xbx1g/Robot/3D_Modeli/Robotska_roka/41002457.jpg

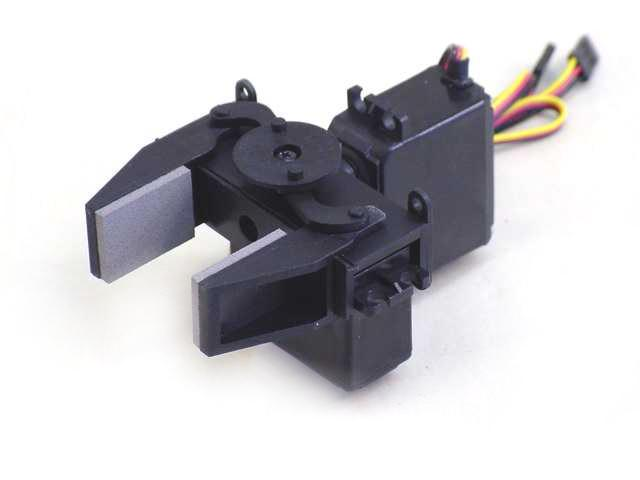
3D_Modeli/Robotska_roka/41002457.jpg
