xbx1g/Robot/3D_Modeli/Robotska_roka/lemotech-ip67-junction-box-250-mm-x-150-mm-x-100-mm-1.snapshot.2/LeMotech IP67 Junction Box, 250 mm x 150 mm x 100 mm D.JPG

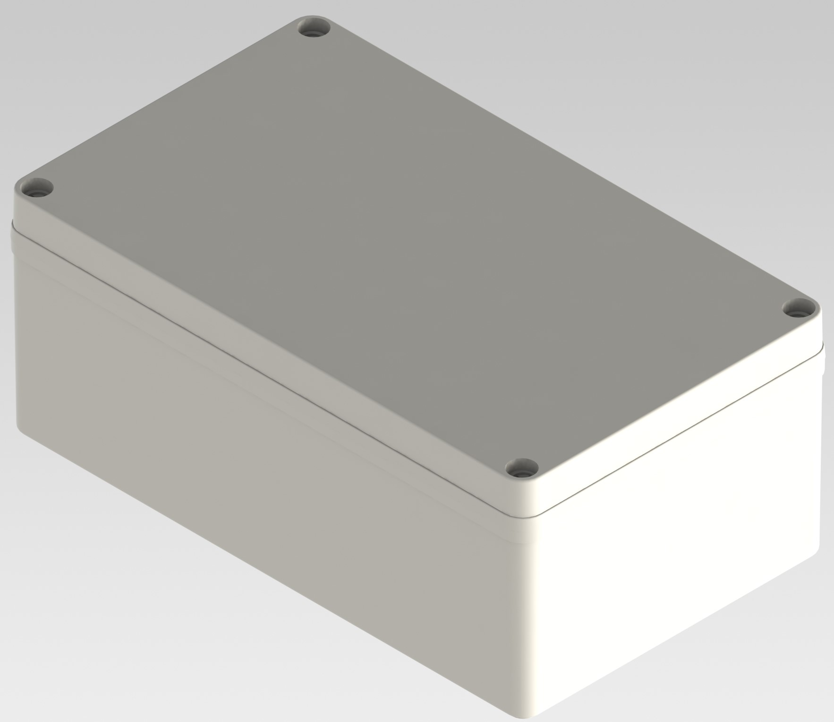
3D_Modeli/Robotska_roka/lemotech-ip67-junction-box-250-mm-x-150-mm-x-100-mm-1.snapshot.2/LeMotech IP67 Junction Box, 250 mm x 150 mm x 100 mm D.JPG
