xbx1g/Robot/3D_Modeli/Robotska_roka/linear-gripper-1.snapshot.4/CAD Model.png

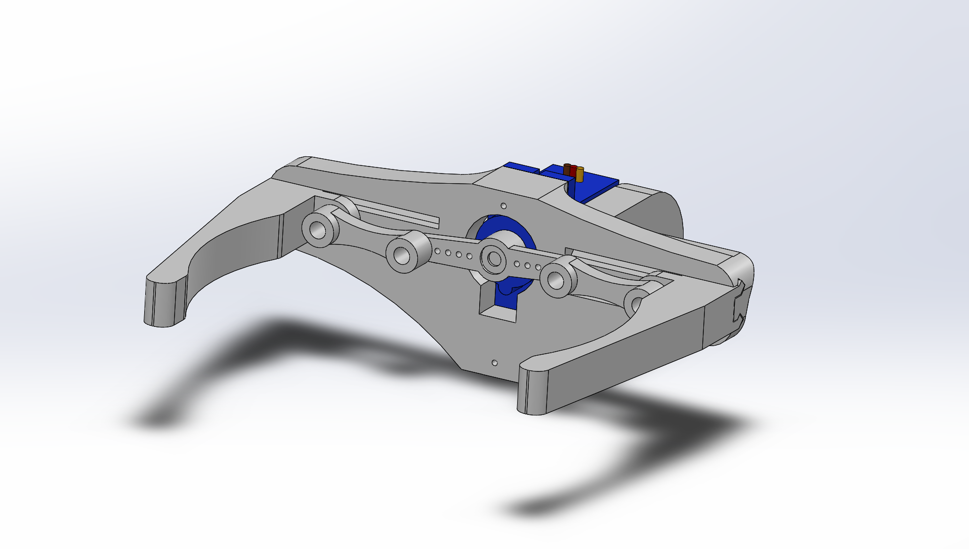
3D_Modeli/Robotska_roka/linear-gripper-1.snapshot.4/CAD Model.png
