xbx1g/Robot/3D_Modeli/Robotska_roka/mecanum-wheel-diameter-100mm-right-1.snapshot.1/Mecanum Wheel (dia 100) Right/Mecanum Wheel (dia 100).jpg

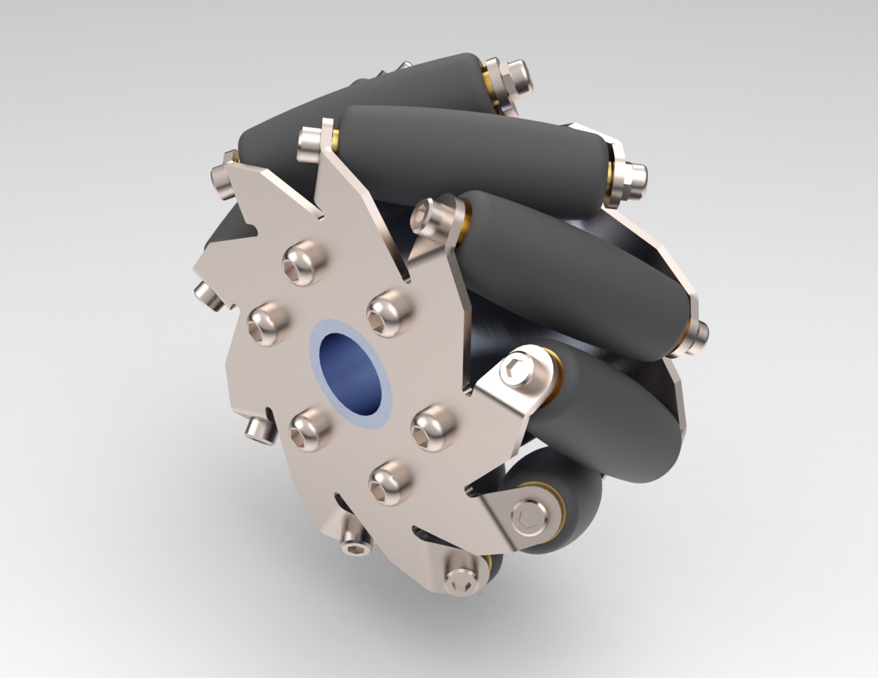
3D_Modeli/Robotska_roka/mecanum-wheel-diameter-100mm-right-1.snapshot.1/Mecanum Wheel (dia 100) Right/Mecanum Wheel (dia 100).jpg
