xbx1g/Robot/Aplikacija/APP INVENTRO/desnogor.png

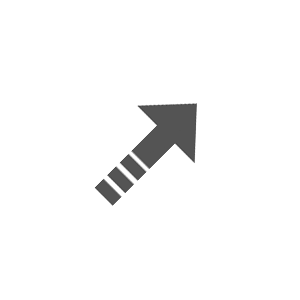
Aplikacija/APP INVENTRO/desnogor.png
