xbx1g/Robot/Aplikacija/APP INVENTRO/levodol.png

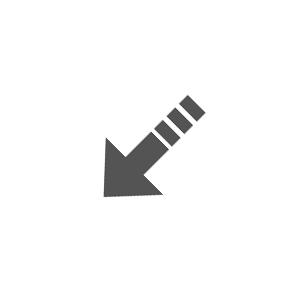
Aplikacija/APP INVENTRO/levodol.png
