xbx1g/Robot/Aplikacija/APP INVENTRO/levogor.png

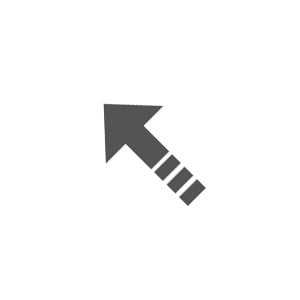
Aplikacija/APP INVENTRO/levogor.png
