xbx1g/Robot/Aplikacija/APP INVENTRO/ozadje.jpg

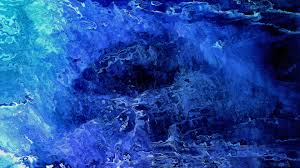
Aplikacija/APP INVENTRO/ozadje.jpg
