xbx1g/Robot/Aplikacija/APP INVENTRO/puscica desno.png

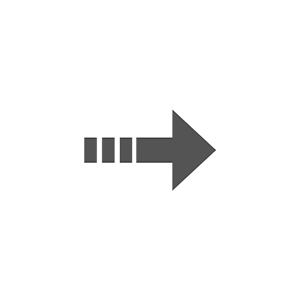
Aplikacija/APP INVENTRO/puscica desno.png
