xbx1g/Robot/Aplikacija/APP INVENTRO/puscica dol.png

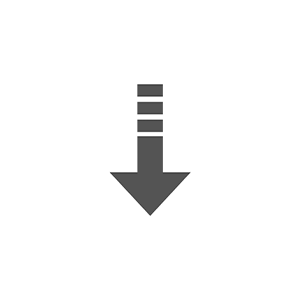
Aplikacija/APP INVENTRO/puscica dol.png
