xbx1g/Robot/Aplikacija/APP INVENTRO/puscica levo.png

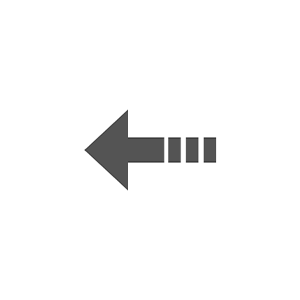
Aplikacija/APP INVENTRO/puscica levo.png
