xbx1g/Robot/Aplikacija/APP INVENTRO/roka.png

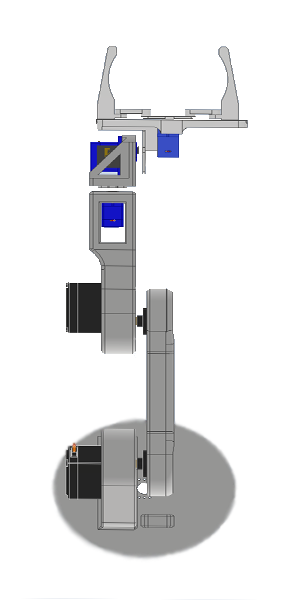
Aplikacija/APP INVENTRO/roka.png
