xbx1g/Robot/Aplikacija/APP INVENTRO/ROTACIJA DESNO.png

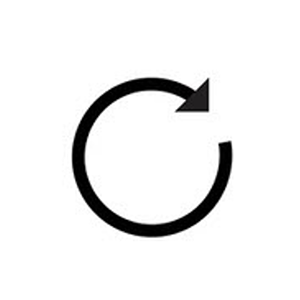
Aplikacija/APP INVENTRO/ROTACIJA DESNO.png
