xbx1g/Robot/Slike/IMG_20231021_095145.jpg

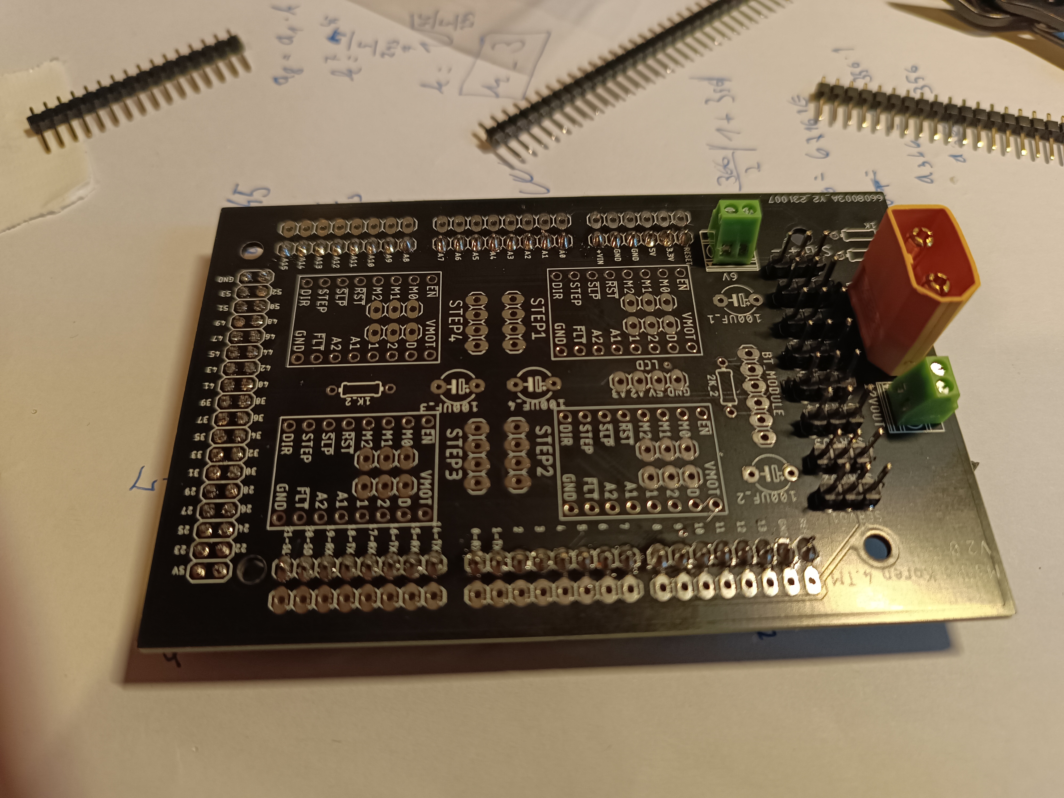
Slike/IMG_20231021_095145.jpg
