xbx1g/Robot/Slike/IMG_20231021_095151.jpg

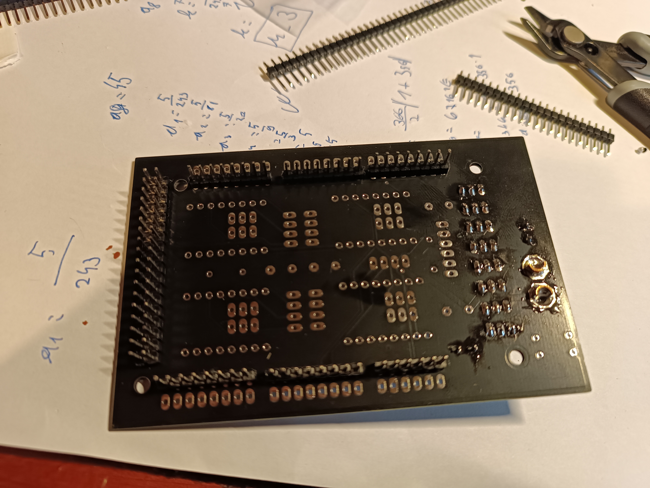
Slike/IMG_20231021_095151.jpg
