xbx1g/Robot/Slike/IMG_20231021_102045.jpg

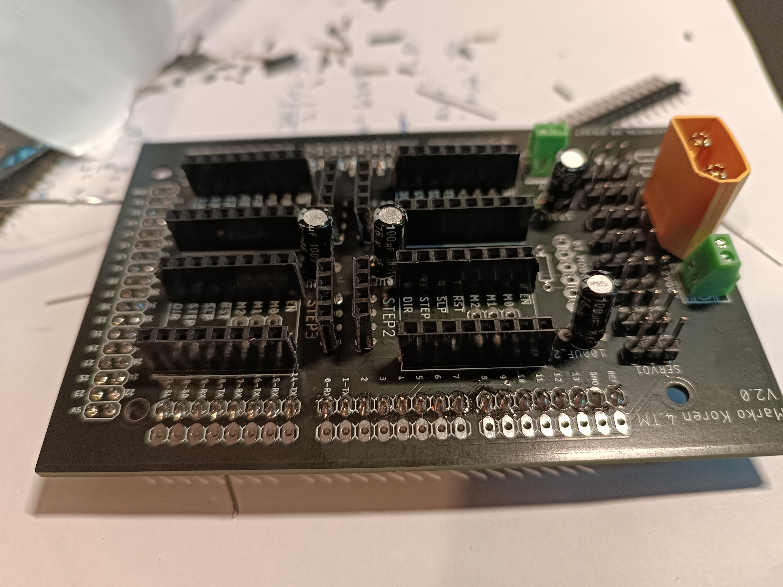
Slike/IMG_20231021_102045.jpg
