xbx1g/Robot/Slike/IMG_20231021_102051.jpg

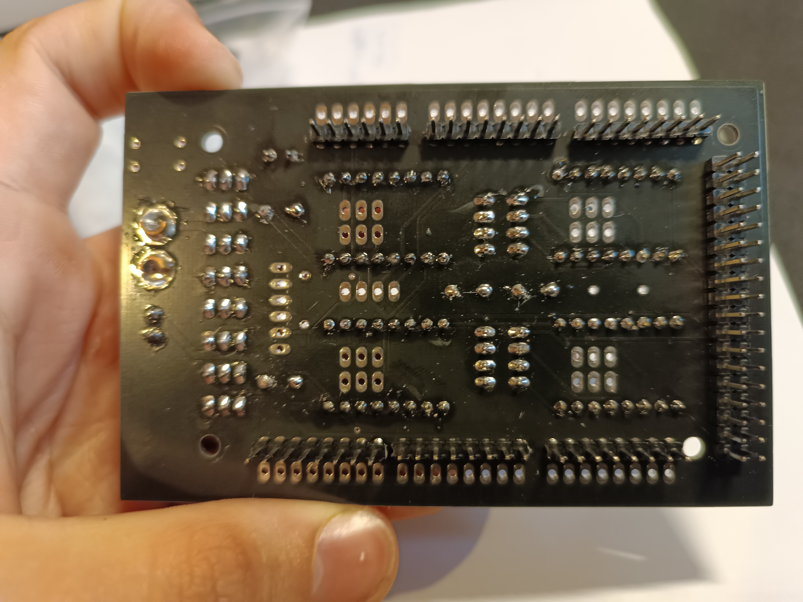
Slike/IMG_20231021_102051.jpg
