xbx1g/Robot/Slike/IMG_20231021_115019.jpg

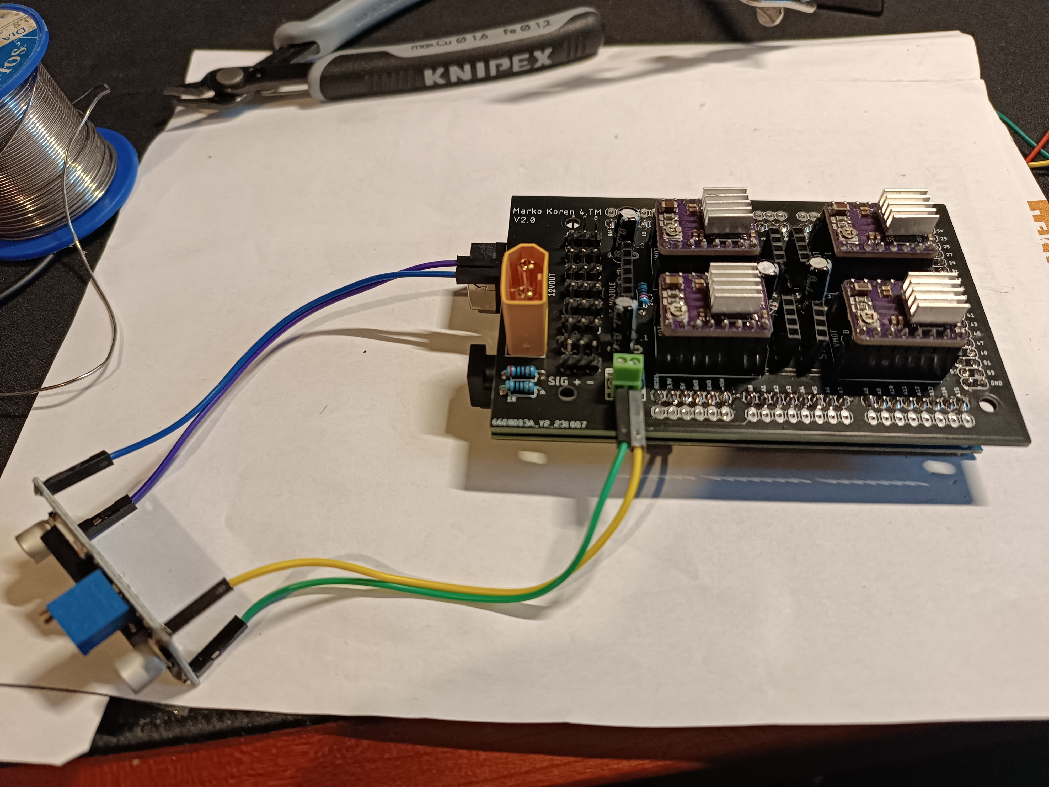
Slike/IMG_20231021_115019.jpg
