xbx1g/Robot/Slike/IMG_20231021_115023.jpg

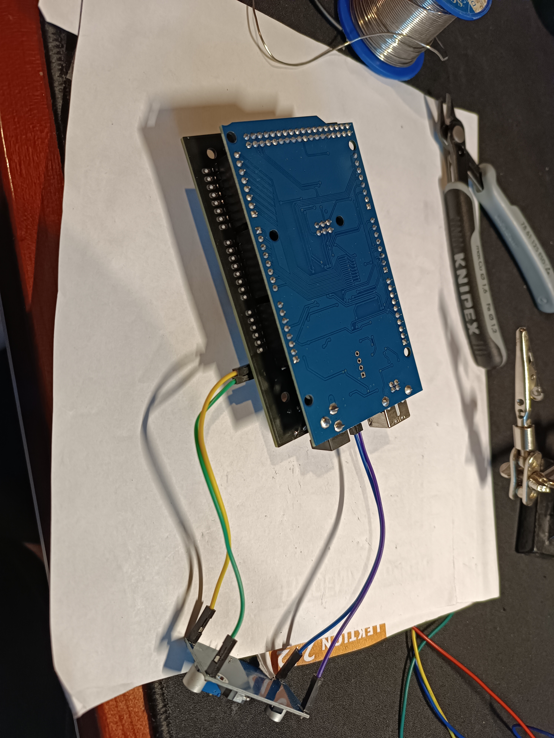
Slike/IMG_20231021_115023.jpg
