xbx1g/Robot/Slike/luknje_1.jpg

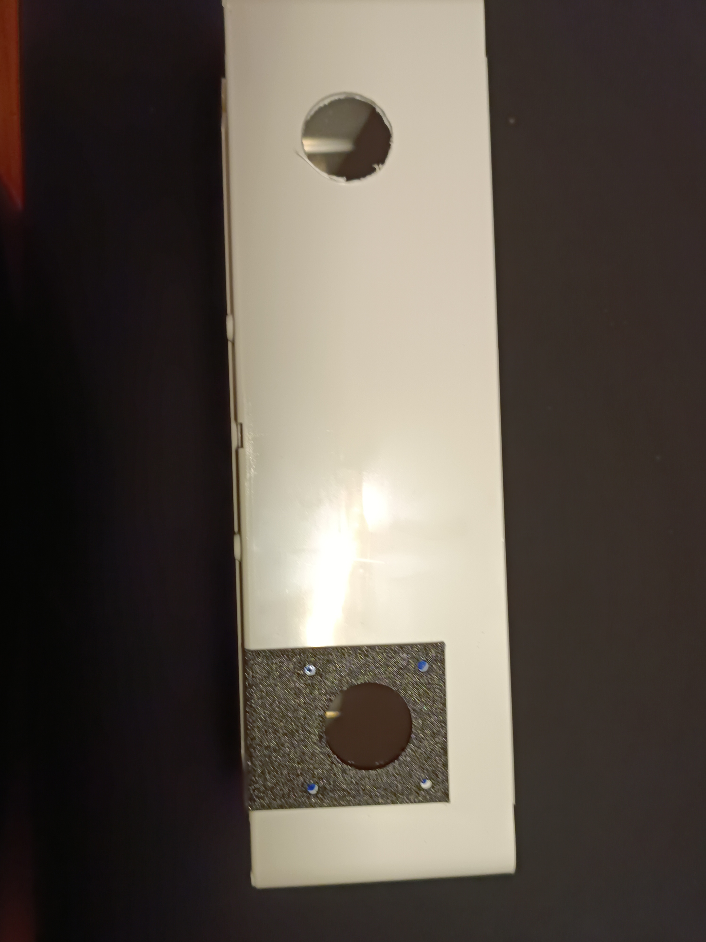
Slike/luknje_1.jpg
