xbx1g/Robot/Slike/luknje_2.jpg

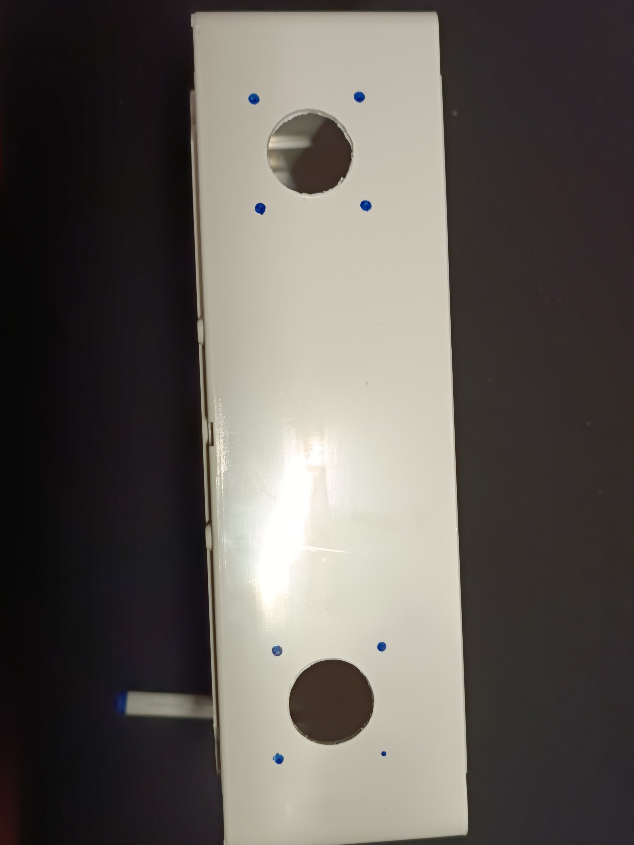
Slike/luknje_2.jpg
