xbx1g/Robot/Slike/luknje_3.jpg

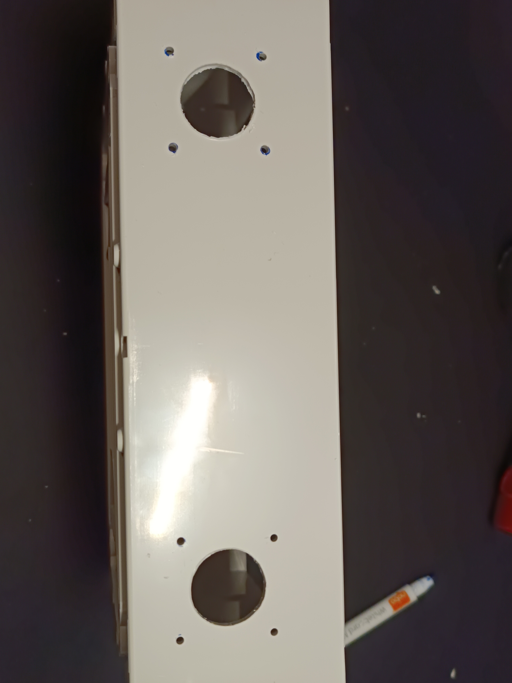
Slike/luknje_3.jpg
