xbx1g/Robot/Slike/pcb_cena.png

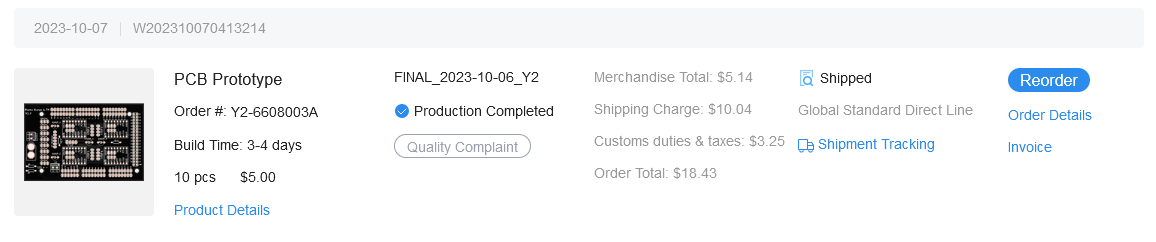
Slike/pcb_cena.png
