xbx1g/Robot/Slike/postavitev_podvozja.jpg

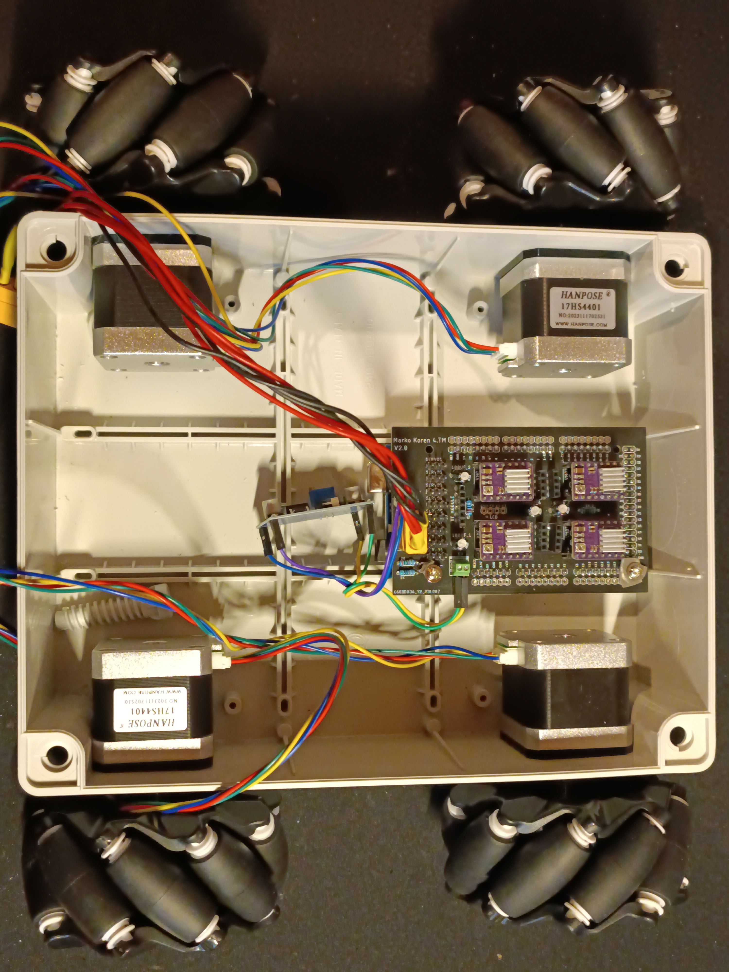
Slike/postavitev_podvozja.jpg
