xbx1g/Robot/Slike/Povezava_z_mecanum_kolesi.jpg

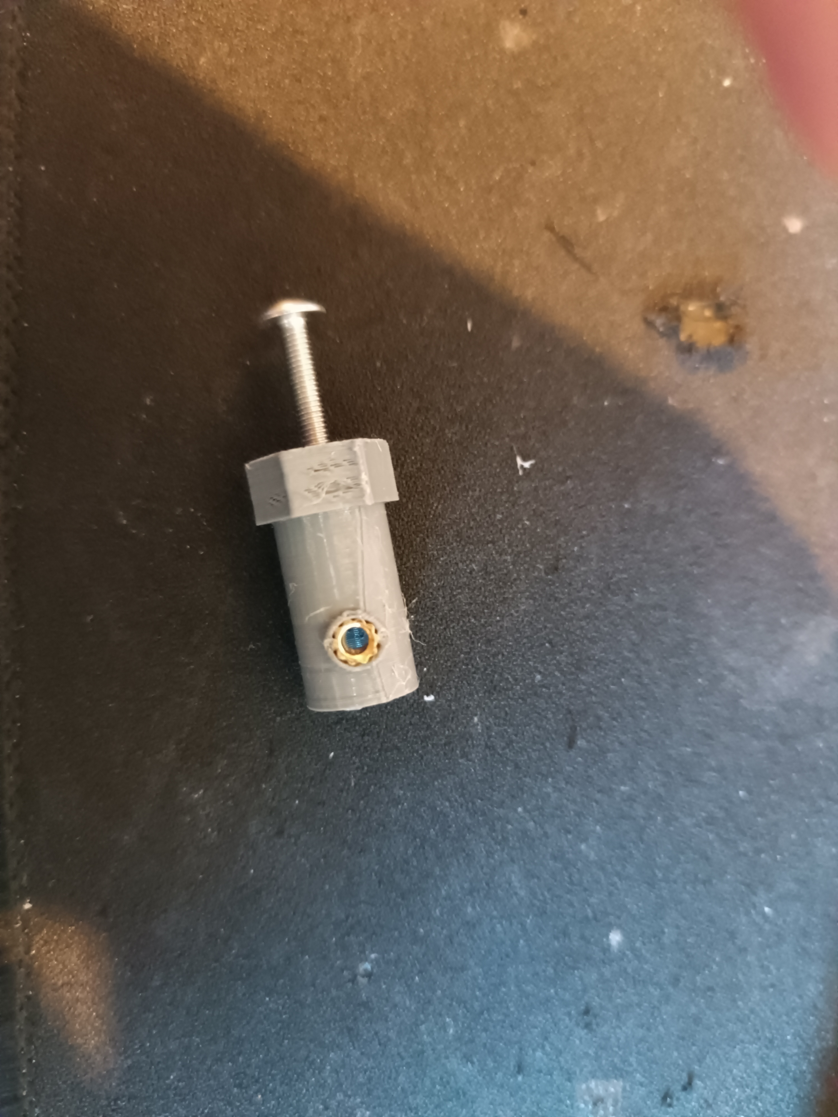
Slike/Povezava_z_mecanum_kolesi.jpg
