xbx1g/Robot/Slike/Robotska_roka_sestavljena (1).jpg

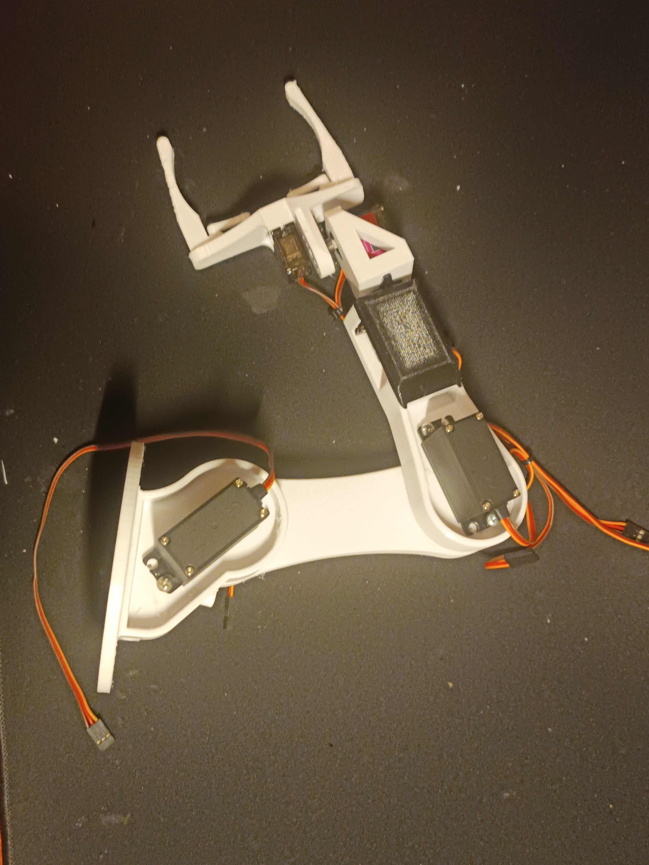
Slike/Robotska_roka_sestavljena (1).jpg
