xbx1g/Robot/Slike/Robotska_roka_sestavljena (2).jpg

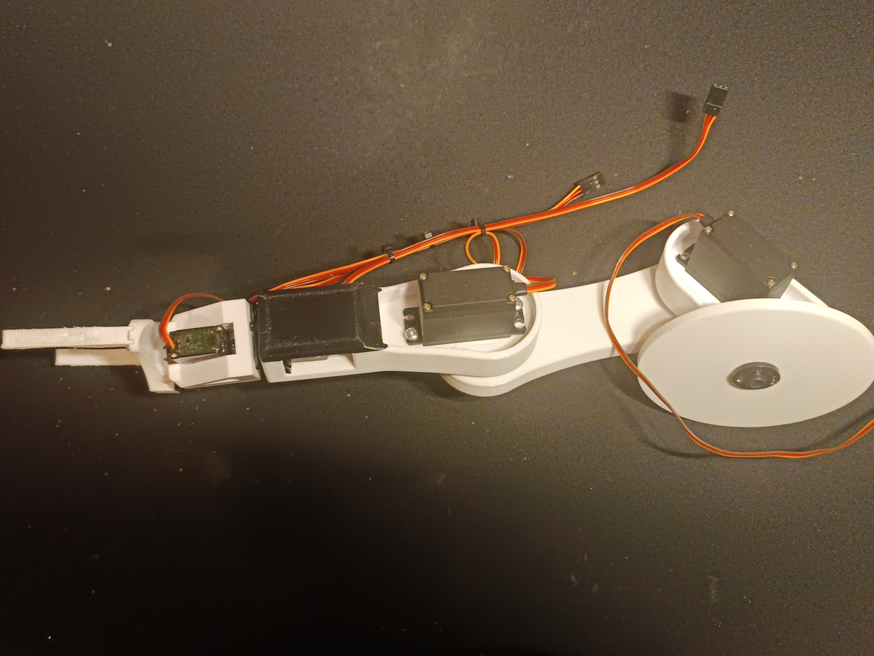
Slike/Robotska_roka_sestavljena (2).jpg
