xbx1g/Robot/Slike/Robotska_roka_sestavljena (3).jpg

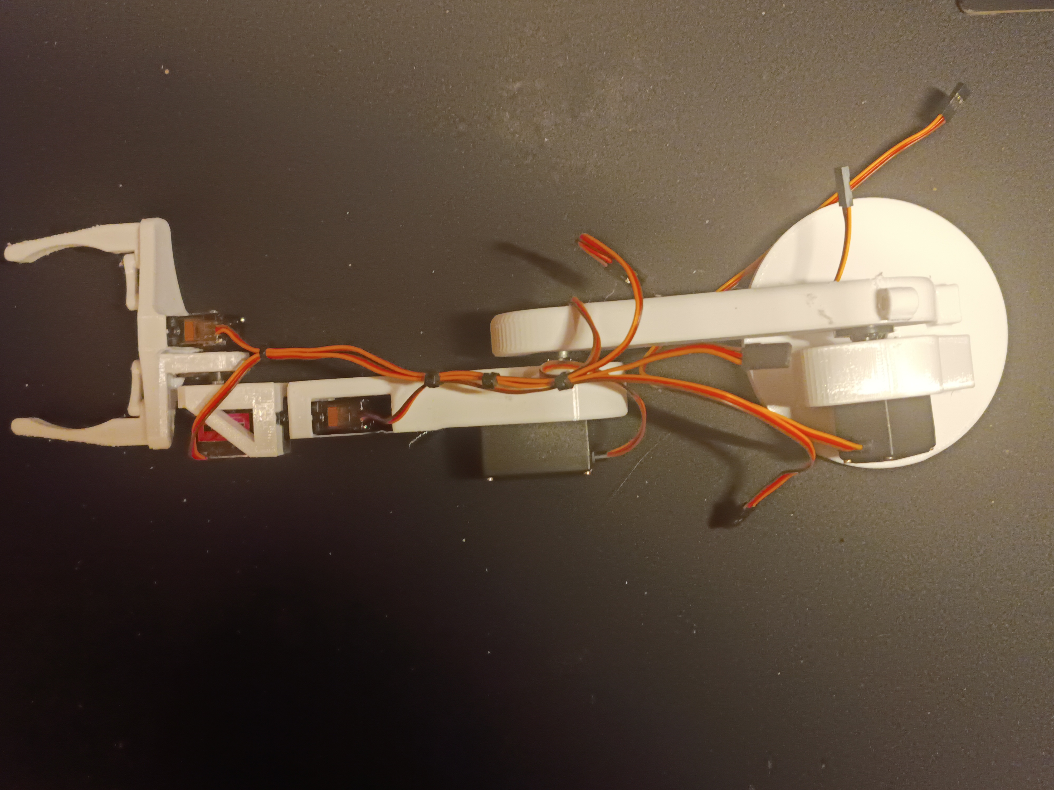
Slike/Robotska_roka_sestavljena (3).jpg
