xbx1g/Robot/Slike/spajanje_steper_motor.jpg

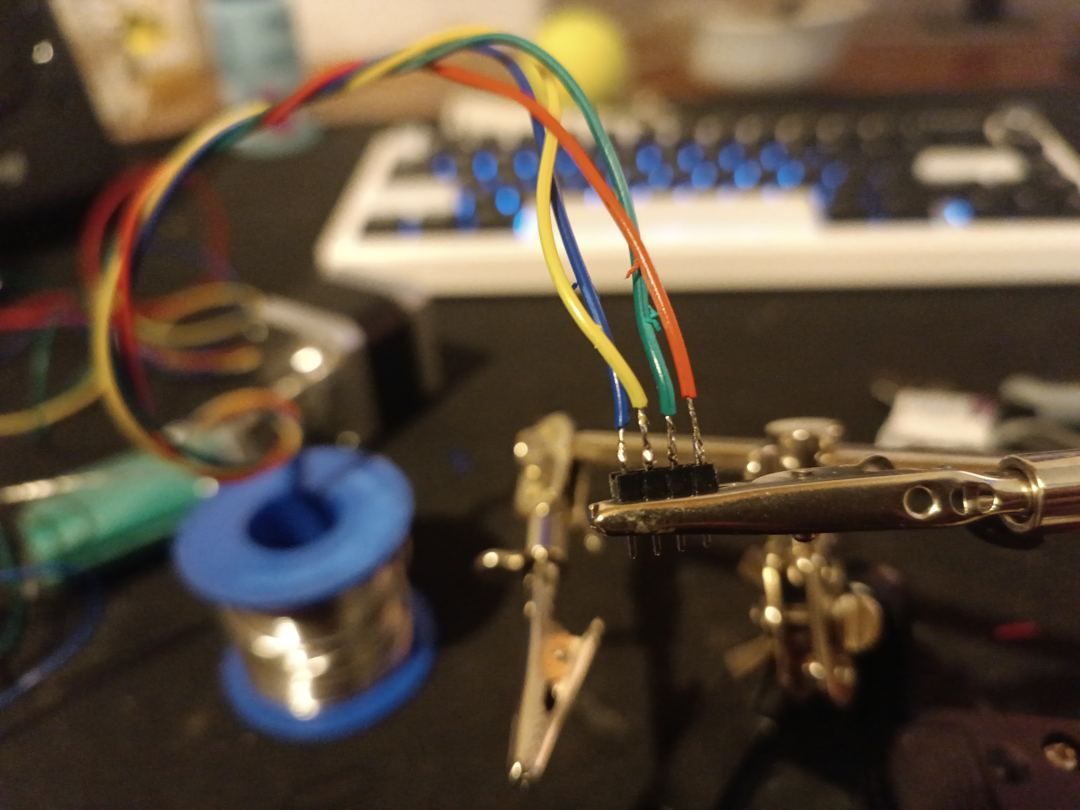
Slike/spajanje_steper_motor.jpg
