xbx1g/Robot/Slike/temperatura_30min.jpg

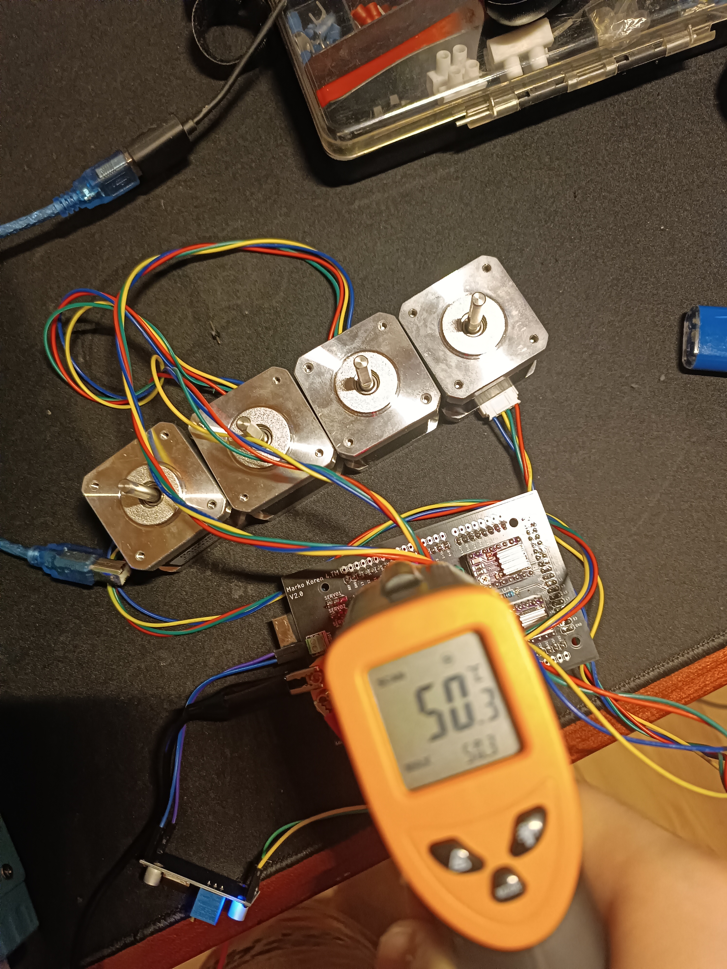
Slike/temperatura_30min.jpg
