xbx1g/Robot/3D_Modeli/VER2/roka2.stl

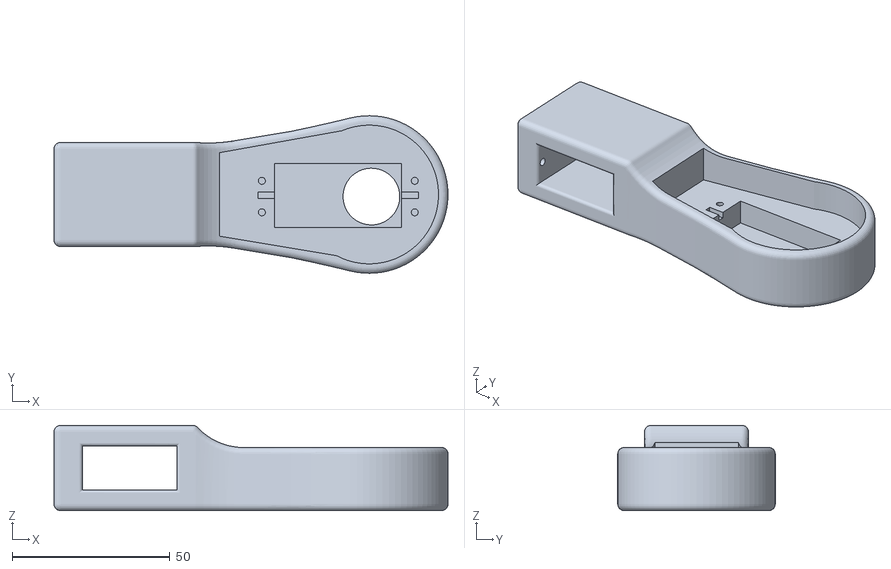
[picture p57: CAD file, 2025-09-28]
3D_Modeli/VER2/roka2.stl
125.0 x 50.0 x 27.0
