xbx1g/Robot/3D_Modeli/VER2/sg90-micro-servo-9g-tower-pro-1.snapshot.3/SG90 - Micro Servo 9g - Tower Pro.5.SLDPRT

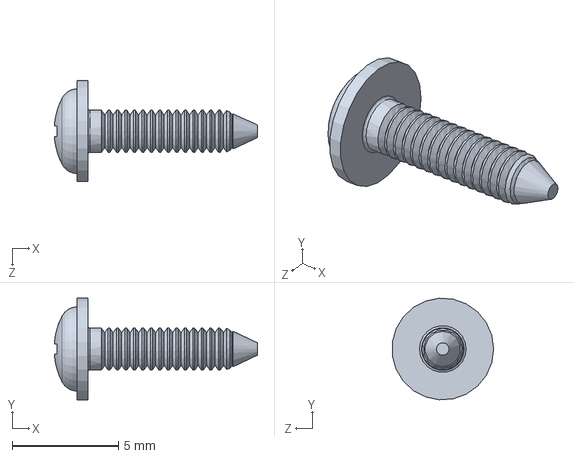
[picture p58: CAD file, 2025-09-28]
3D_Modeli/VER2/sg90-micro-servo-9g-tower-pro-1.snapshot.3/SG90 - Micro Servo 9g - Tower Pro.5.SLDPRT
9.57 x 4.79 x 4.78 mm
