xbx1g/Robot/3D_Modeli/Robotska_roka/123.stl

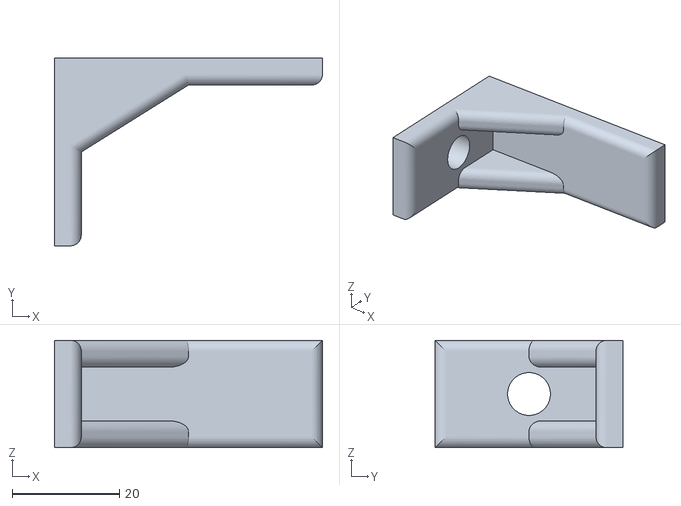
[picture p59: CAD file, 2025-09-28]
3D_Modeli/Robotska_roka/123.stl
50.0 x 35.0 x 20.0
