xbx1g/Robot/3D_Modeli/Robotska_roka/lemotech-ip67-junction-box-250-mm-x-150-mm-x-100-mm-1.snapshot.2/Cover, LeMotech IP67 Junction Box, 250 mm x 150 mm x 100 mm.SLDPRT

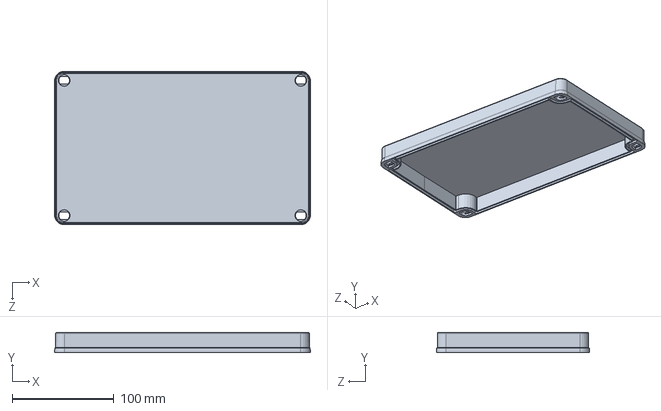
[picture p60: CAD file, 2025-09-28]
3D_Modeli/Robotska_roka/lemotech-ip67-junction-box-250-mm-x-150-mm-x-100-mm-1.snapshot.2/Cover, LeMotech IP67 Junction Box, 250 mm x 150 mm x 100 mm.SLDPRT
252.0 x 20.0 x 151.0 mm
