xbx1g/Robot/3D_Modeli/Robotska_roka/mecanum-wheel-diameter-100mm-right-1.snapshot.1/Mecanum Wheel (dia 100) Right/Components/Roller Bracket.SLDPRT

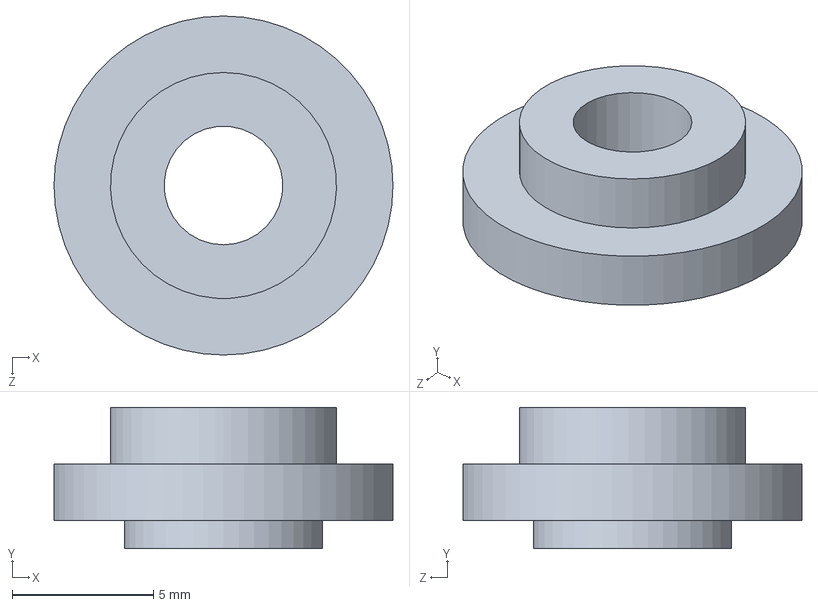
[picture p61: CAD file, 2025-09-28]
3D_Modeli/Robotska_roka/mecanum-wheel-diameter-100mm-right-1.snapshot.1/Mecanum Wheel (dia 100) Right/Components/Roller Bracket.SLDPRT
12.0 x 5.00 x 12.0 mm
