xbx1g/Robot/3D_Modeli/VER2/buh.stl

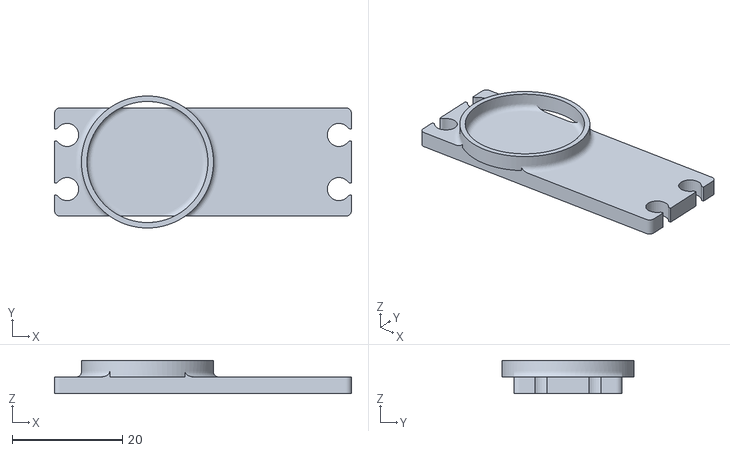
[picture p63: CAD file, 2025-09-28]
3D_Modeli/VER2/buh.stl
54.0 x 24.0 x 6.00
