xbx1g/Robot/3D_Modeli/VER2/linear-gripper-1.snapshot.4/Linear Gripper/Part1.stl

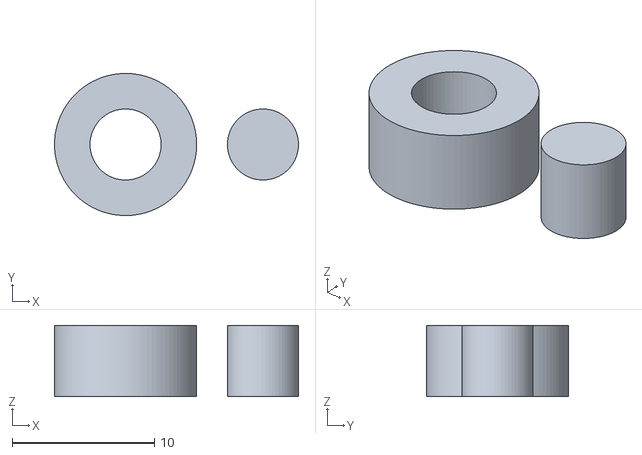
[picture p64: CAD file, 2025-09-28]
3D_Modeli/VER2/linear-gripper-1.snapshot.4/Linear Gripper/Part1.stl
17.2 x 10.00 x 5.00
