xbx1g/Robot/3D_Modeli/VER2/mecanum-wheel-diameter-100mm-right-1.snapshot.1/Mecanum Wheel (dia 100) Right/Components/Shaft.SLDPRT

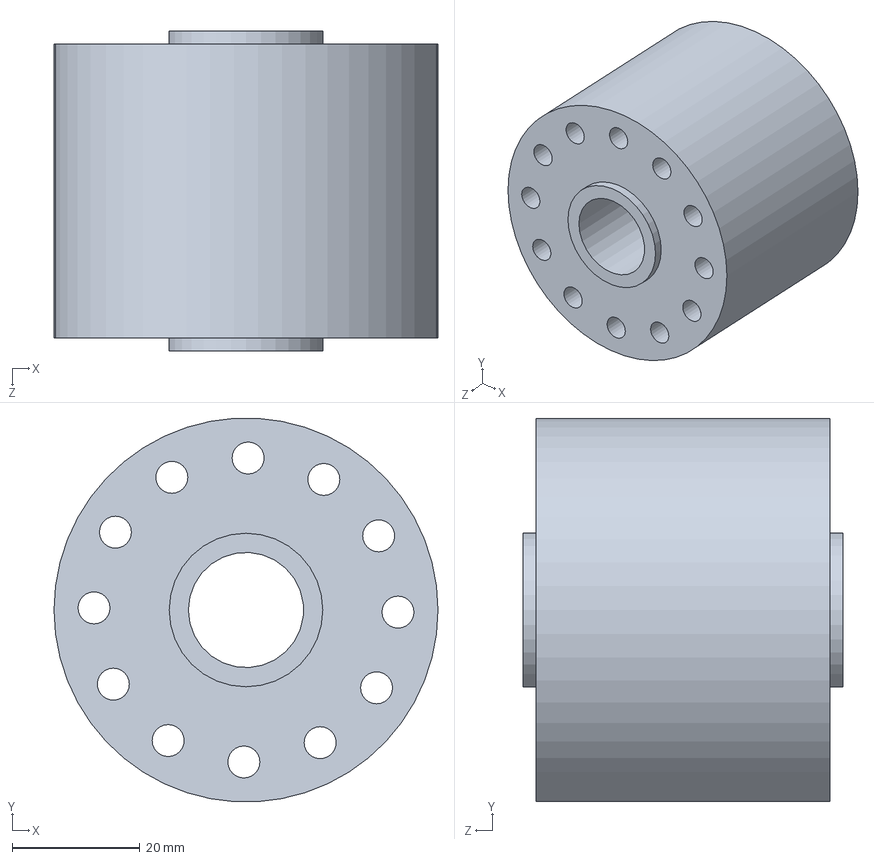
[picture p65: CAD file, 2025-09-28]
3D_Modeli/VER2/mecanum-wheel-diameter-100mm-right-1.snapshot.1/Mecanum Wheel (dia 100) Right/Components/Shaft.SLDPRT
60.0 x 59.9 x 50.0 mm
