xbx1g/Robot/3D_Modeli/Robotska_roka/linear-gripper-1.snapshot.4/Linear Gripper/Linear Base.stl

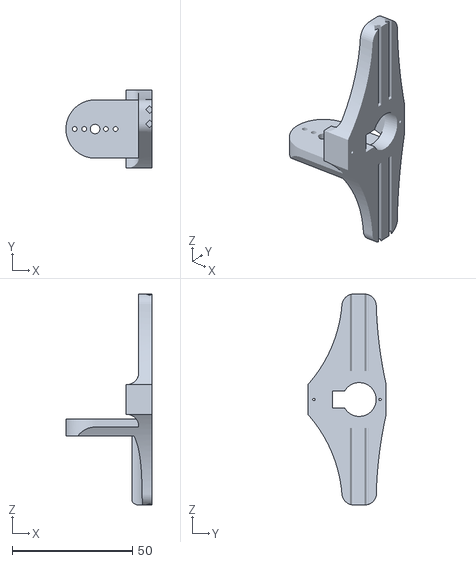
[picture p66: CAD file, 2025-09-28]
3D_Modeli/Robotska_roka/linear-gripper-1.snapshot.4/Linear Gripper/Linear Base.stl
35.8 x 32.6 x 87.8
