xbx1g/Robot/3D_Modeli/Robotska_roka/linear-gripper-1.snapshot.4/STL for 3D Printing/Linear Gripper - Linear Link-1.STL

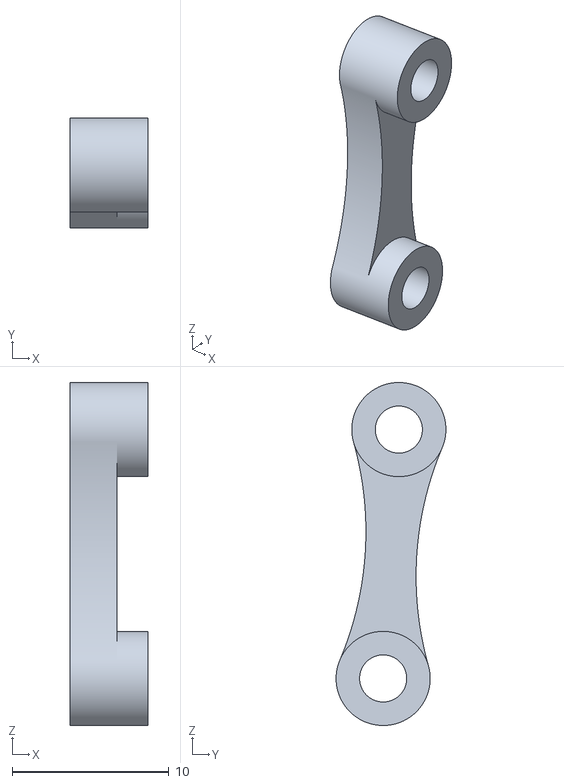
[picture p67: CAD file, 2025-09-28]
3D_Modeli/Robotska_roka/linear-gripper-1.snapshot.4/STL for 3D Printing/Linear Gripper - Linear Link-1.STL
5.00 x 7.00 x 21.9
