xbx1g/Robot/3D_Modeli/Robotska_roka/mecanum-wheel-diameter-100mm-right-1.snapshot.1/Mecanum Wheel (dia 100) Right/Components/Roller.SLDPRT

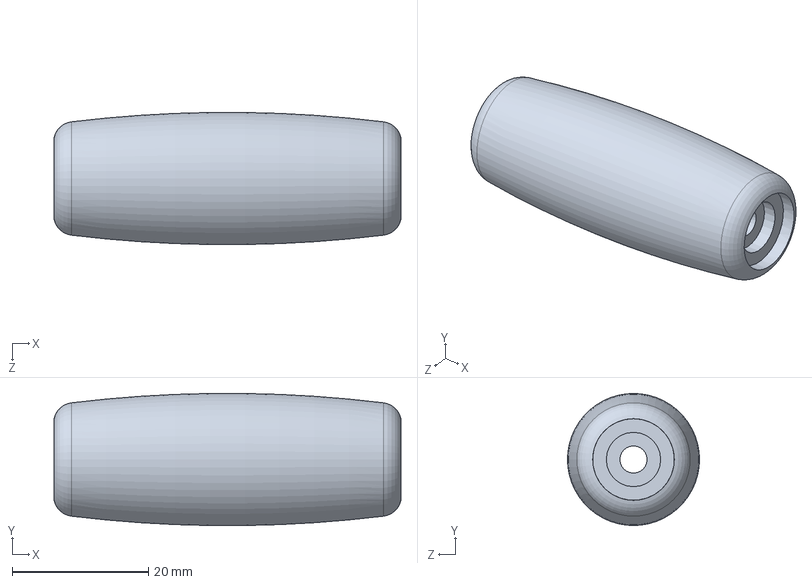
[picture p68: CAD file, 2025-09-28]
3D_Modeli/Robotska_roka/mecanum-wheel-diameter-100mm-right-1.snapshot.1/Mecanum Wheel (dia 100) Right/Components/Roller.SLDPRT
51.0 x 19.4 x 19.4 mm
