xbx1g/Robot/3D_Modeli/Robotska_roka/PIN.stl

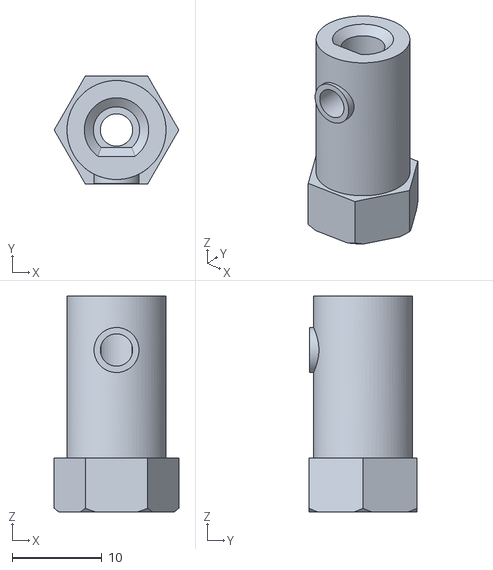
[picture p69: CAD file, 2025-09-28]
3D_Modeli/Robotska_roka/PIN.stl
13.9 x 12.0 x 24.0
