xbx1g/Robot/3D_Modeli/Robotska_roka/roka3.3mf

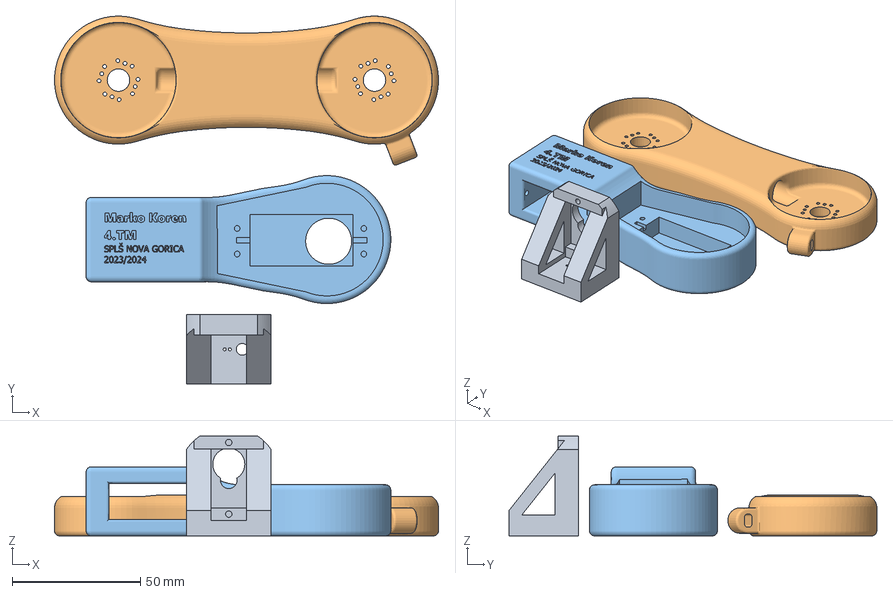
[picture p70: CAD file, 2025-09-28]
3D_Modeli/Robotska_roka/roka3.3mf
150.0 x 143.6 x 39.0 mm
roka3.stl
roka1.stl
roka2.stl
