xbx1g/Robot/3D_Modeli/Robotska_roka/sg90-micro-servo-9g-tower-pro-1.snapshot.3/SG90 - Micro Servo 9g - Tower Pro.4.SLDPRT

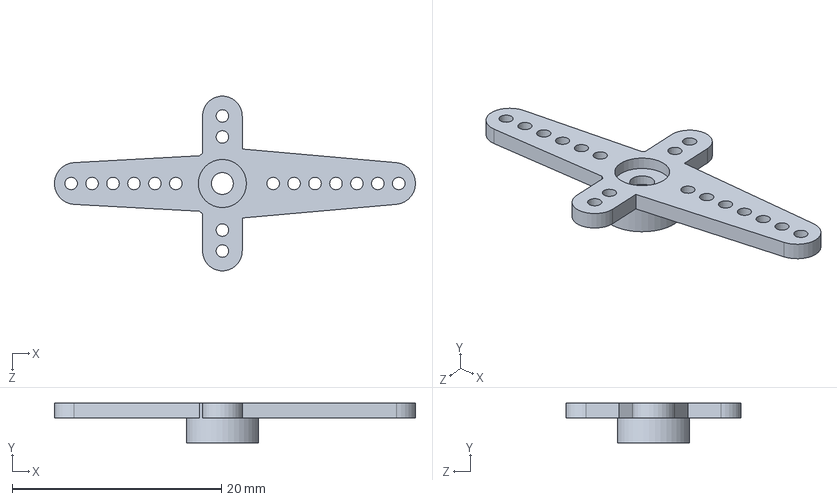
[picture p71: CAD file, 2025-09-28]
3D_Modeli/Robotska_roka/sg90-micro-servo-9g-tower-pro-1.snapshot.3/SG90 - Micro Servo 9g - Tower Pro.4.SLDPRT
34.5 x 3.80 x 16.7 mm
