xbx1g/Robot/3D_Modeli/Robotska_roka/linear-gripper-1.snapshot.4/Linear Gripper/LGrip.3mf

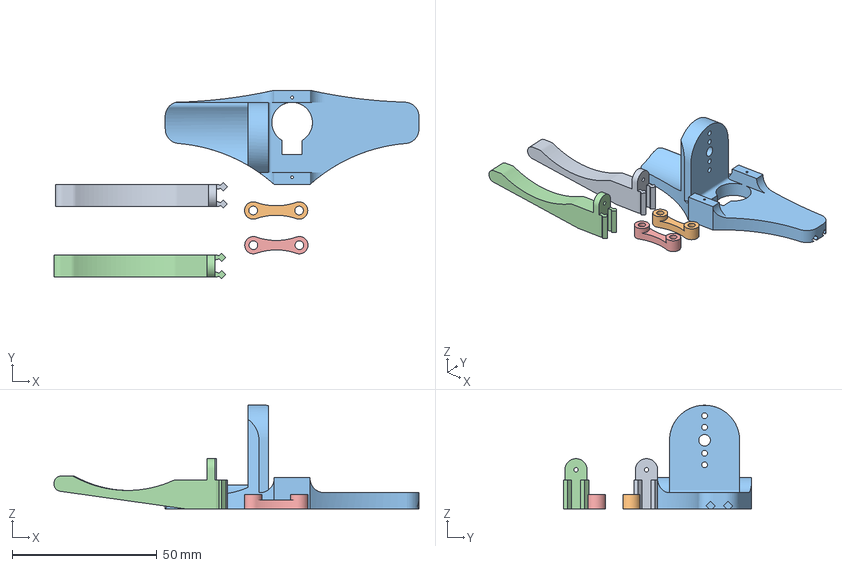
[picture p72: CAD file, 2025-09-28]
3D_Modeli/Robotska_roka/linear-gripper-1.snapshot.4/Linear Gripper/LGrip.3mf
126.3 x 65.2 x 35.8 mm
LGrip.stl x 2
Linear Link.stl x 2
Linear Base.stl
