xbx1g/Robot/3D_Modeli/VER2/2.stl

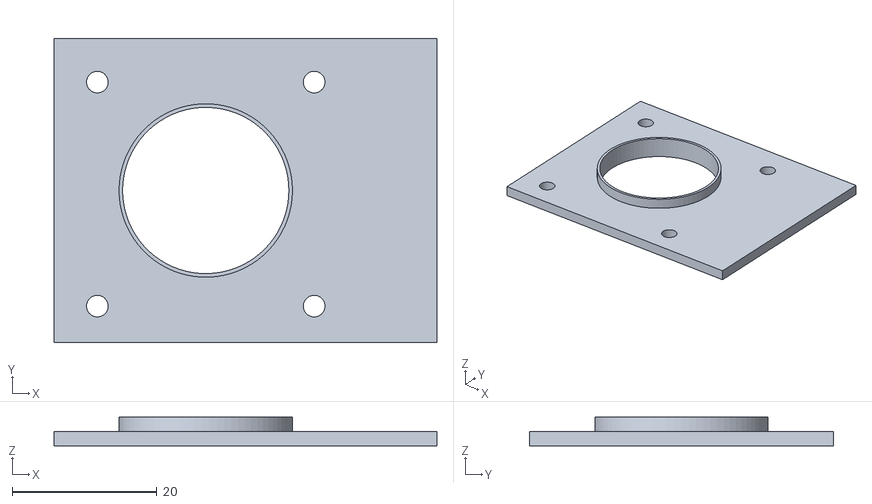
[picture p74: CAD file, 2025-09-28]
3D_Modeli/VER2/2.stl
53.0 x 42.0 x 4.00
