xbx1g/Robot/3D_Modeli/VER2/sg90-micro-servo-9g-tower-pro-1.snapshot.3/SG90 - Micro Servo 9g - Tower Pro.6.SLDPRT

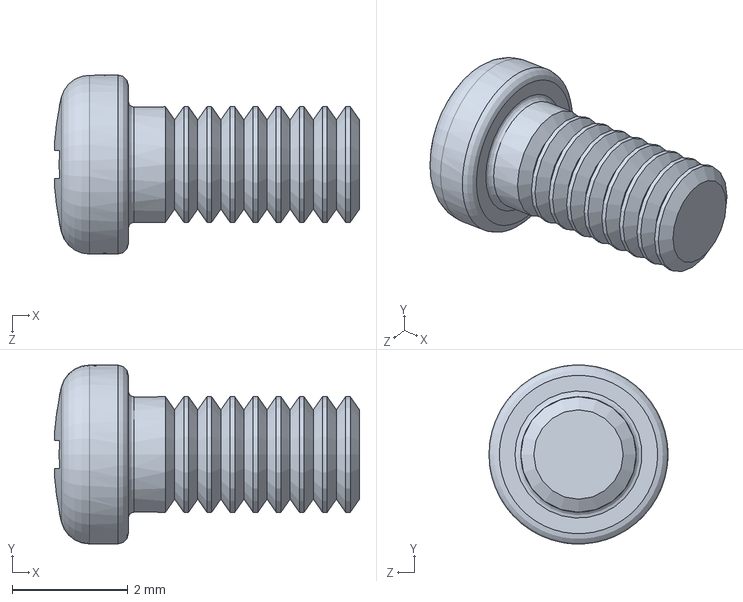
[picture p75: CAD file, 2025-09-28]
3D_Modeli/VER2/sg90-micro-servo-9g-tower-pro-1.snapshot.3/SG90 - Micro Servo 9g - Tower Pro.6.SLDPRT
5.28 x 3.10 x 3.10 mm
