xbx1g/Robot/3D_Modeli/Robotska_roka/buh2.stl

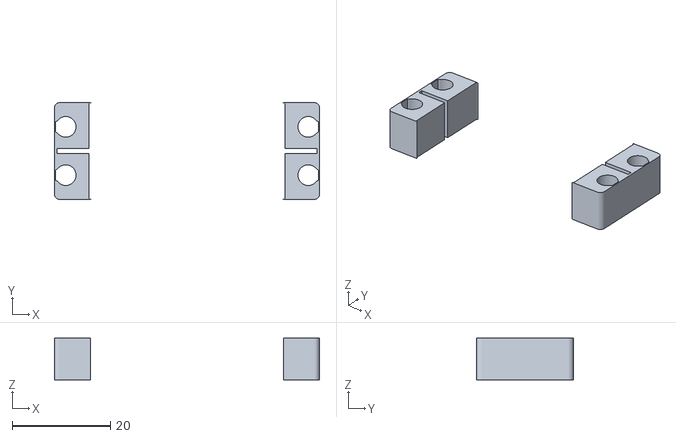
[picture p76: CAD file, 2025-09-28]
3D_Modeli/Robotska_roka/buh2.stl
54.0 x 19.7 x 8.50
