xbx1g/Robot/3D_Modeli/VER2/Part2.stl

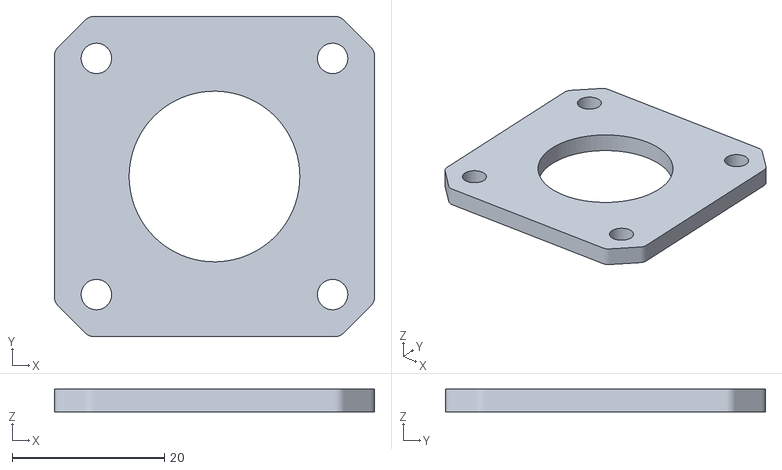
[picture p77: CAD file, 2025-09-28]
3D_Modeli/VER2/Part2.stl
42.0 x 42.0 x 3.00
