xbx1g/Robot/3D_Modeli/VER2/miza.stl

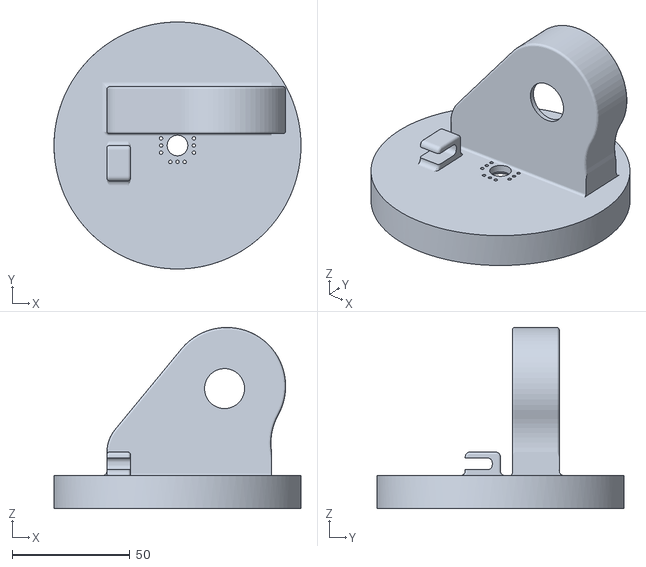
[picture p78: CAD file, 2025-09-28]
3D_Modeli/VER2/miza.stl
105.0 x 105.0 x 77.0
