xbx1g/Robot/Slike/Load_test_12.6V_min.jpg

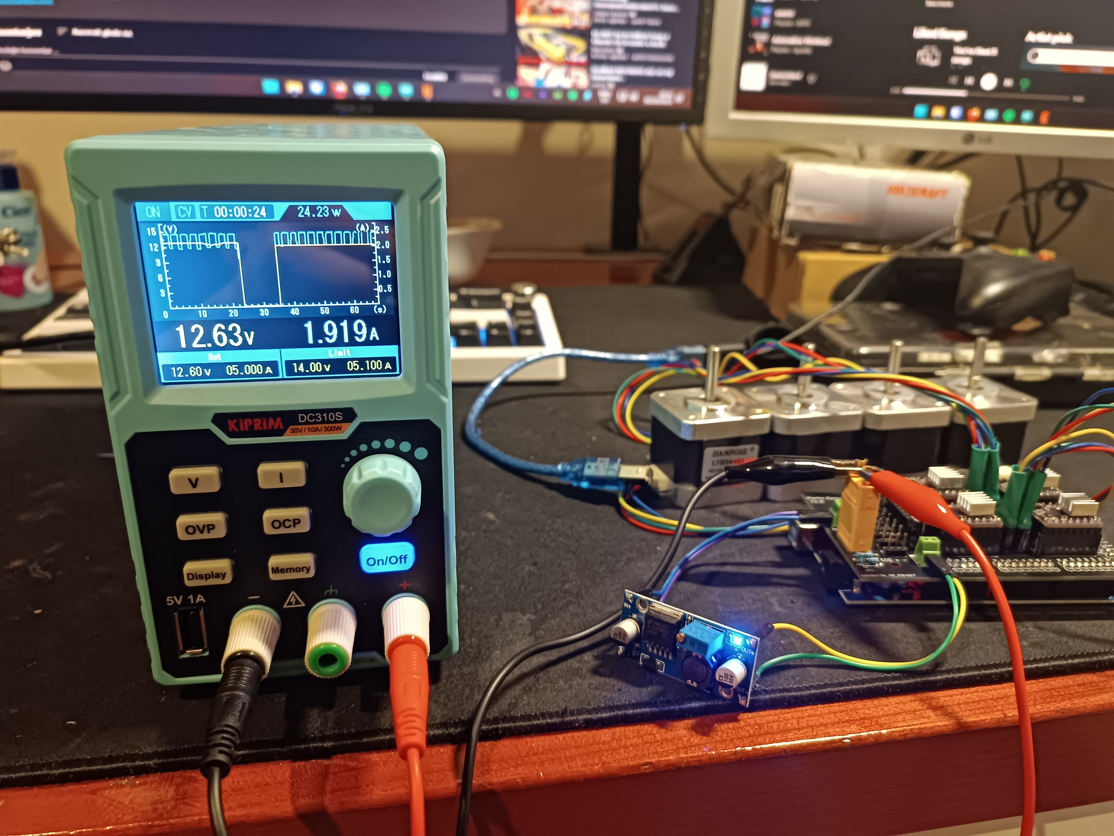
Slike/Load_test_12.6V_min.jpg
