xbx1g/Robot/Slike/Load_test_12V_max.jpg

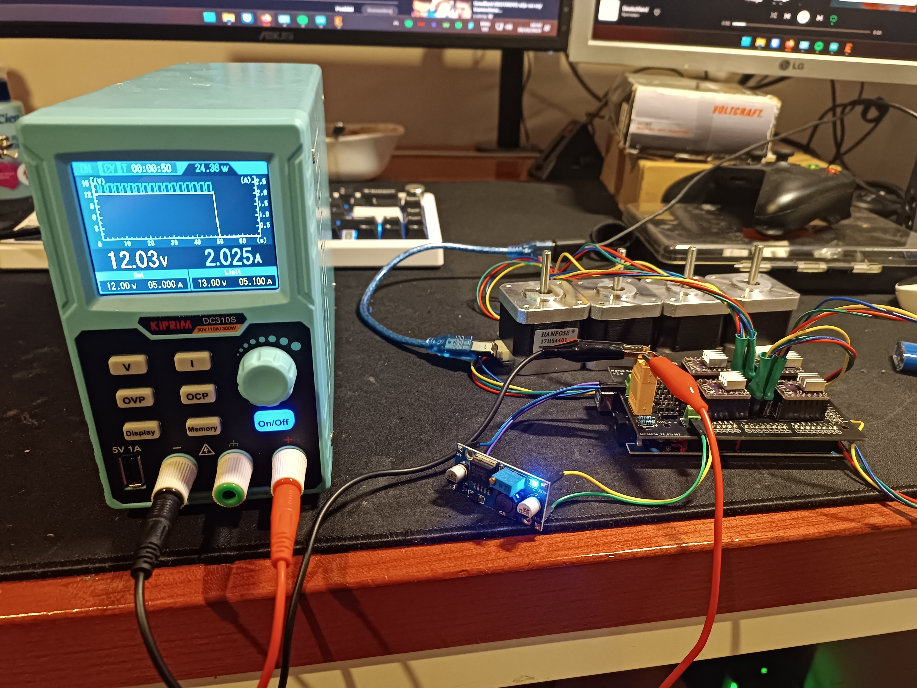
Slike/Load_test_12V_max.jpg
