xbx1g/Robot/Slike/Load_test_12V_min.jpg

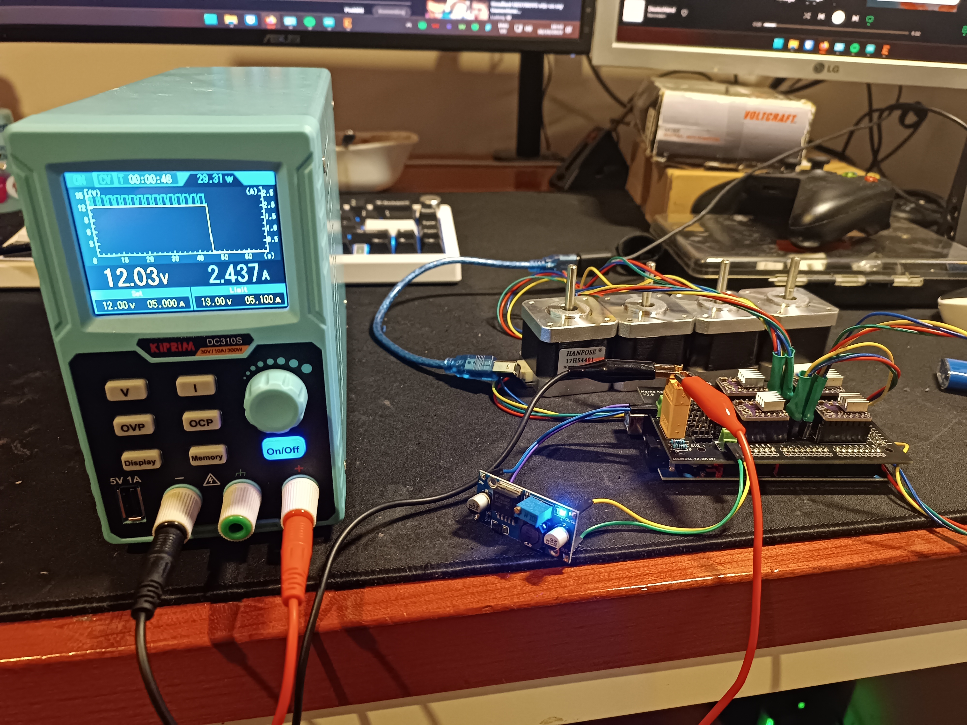
Slike/Load_test_12V_min.jpg
