xbx1g/Robot/Aplikacija/glavni_program/prei.ino

void preimenovanje() {
  dataIn = BT.read();
  Serial.println(dataIn);
  if (dataIn == 0) {
    korak = 0;
  }
  if (dataIn == 1) {
    korak = 1;
  }
  if (dataIn == 2) {
    korak = 2;
  }
  if (dataIn == 3) {
    korak = 3;
  }
  if (dataIn == 4) {
    korak = 4;
  }
  if (dataIn == 5) {
    korak = 5;
  }
  if (dataIn == 6) {
    korak = 6;
  }
  if (dataIn == 7) {
    korak = 7;
  }
  if (dataIn == 8) {
    korak = 8;
  }
  if (dataIn == 9) {
    korak = 9;
  }
  if (dataIn == 10) {
    korak = 10;
  }
  if (dataIn == 11) {
    korak = 11;
  }
  if (dataIn == 12) {
    korak = 12;
  }
  if (dataIn == 14) {
    korak = 14;
  }
  if (dataIn == 16) {
    korak = 16;
  }
  if (dataIn == 17) {
    korak = 17;
  }
  if (dataIn == 18) {
    korak = 18;
  }
  if (dataIn == 19) {
    korak = 19;
  }
  if (dataIn == 20) {
    korak = 20;
  }
  if (dataIn == 21) {
    korak = 21;
  }
  if (dataIn == 22) {
    korak = 22;
  }
  if (dataIn == 23) {
    korak = 23;
  }
  if (dataIn == 24) {
    korak = 24;
  }
  if (dataIn == 25) {
    korak = 25;
  }
  if (dataIn == 26) {
    korak = 26;
  }
  if (dataIn == 27) {
    korak = 27;
  }
}
